marksard/Keyboards/_image/oled01.jpg

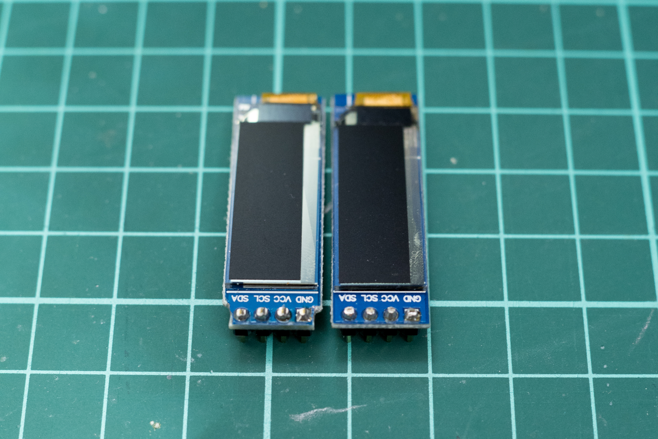
_image/oled01.jpg
