marksard/Keyboards/leftover30/documents/_image/case.png

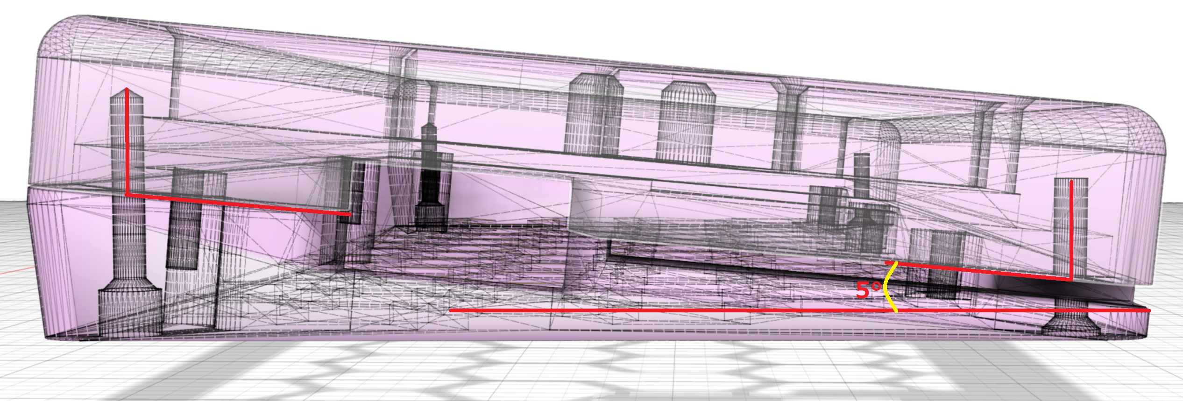
leftover30/documents/_image/case.png
