marksard/Keyboards/leftover30/documents/_image/case_bottom.jpg

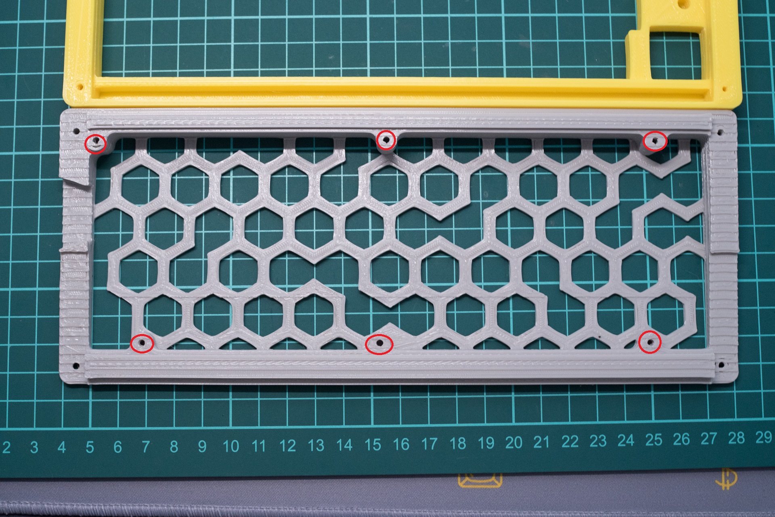
leftover30/documents/_image/case_bottom.jpg
