marksard/Keyboards/leftover30/documents/_image/case_ins1.jpg

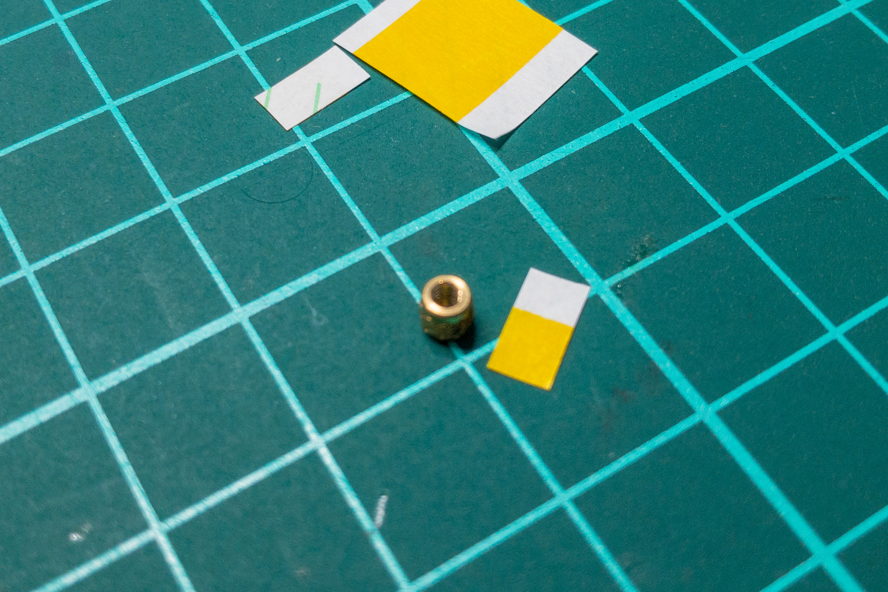
leftover30/documents/_image/case_ins1.jpg
