marksard/Keyboards/leftover30/documents/_image/case_ins2.jpg

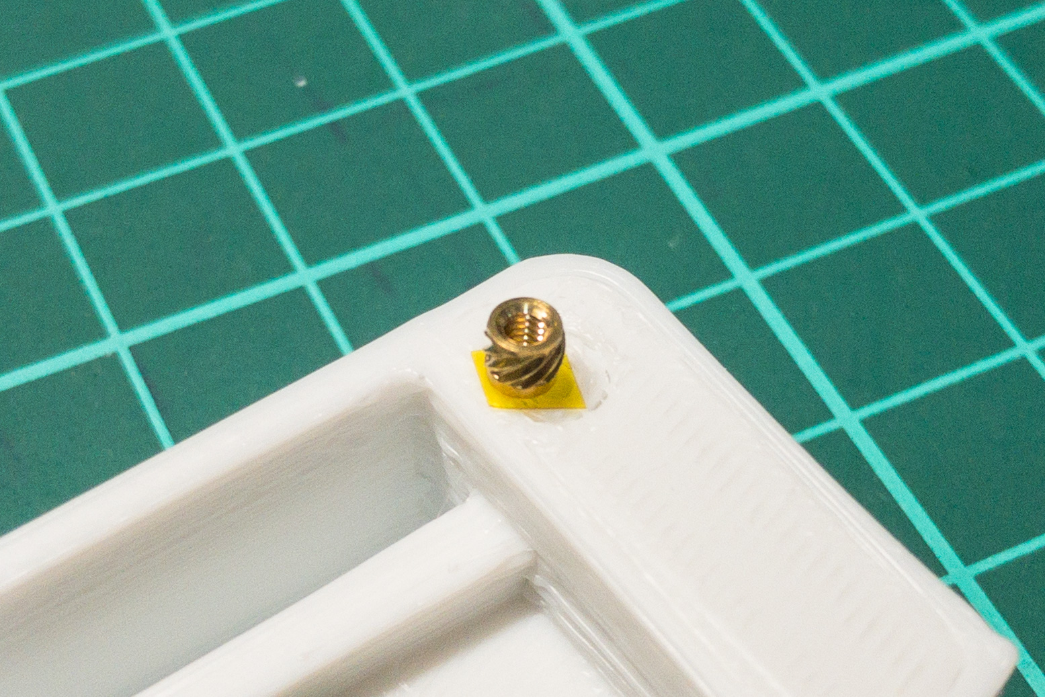
leftover30/documents/_image/case_ins2.jpg
