marksard/Keyboards/leftover30/documents/_image/case_top.jpg

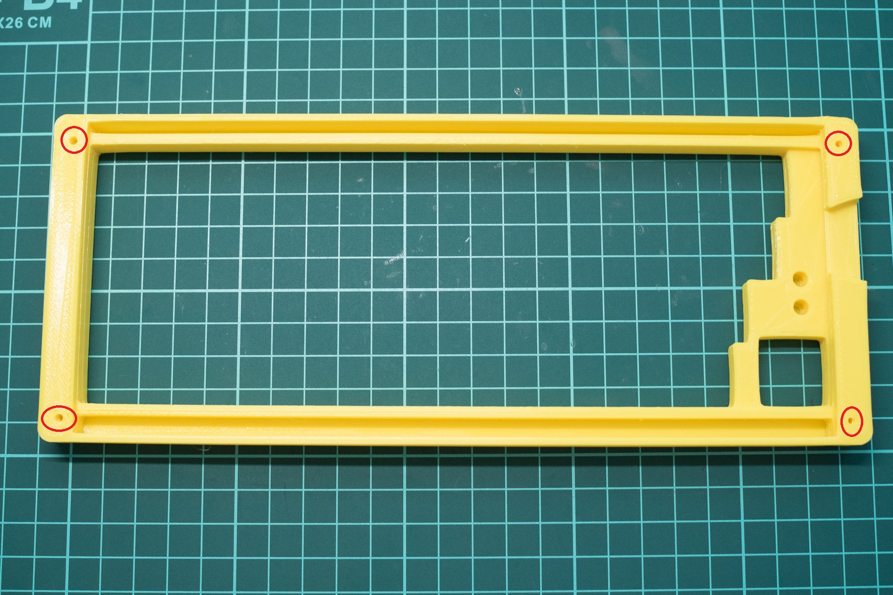
leftover30/documents/_image/case_top.jpg
