marksard/Keyboards/leftover30/documents/_image/diode2.jpg

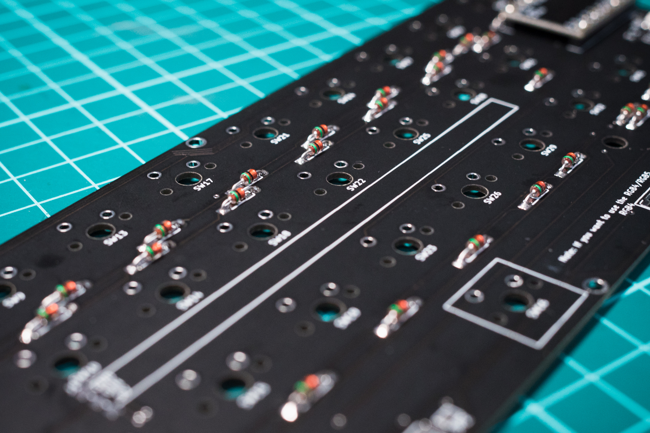
leftover30/documents/_image/diode2.jpg
