marksard/Keyboards/leftover30/documents/_image/led4.jpg

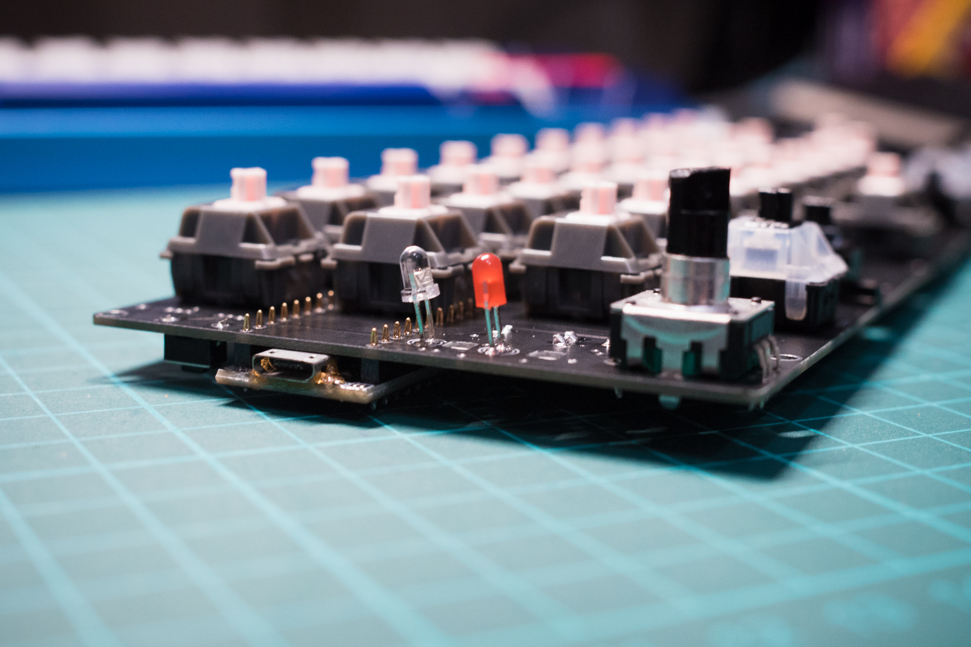
leftover30/documents/_image/led4.jpg
