marksard/Keyboards/leftover30/documents/_image/led.jpg

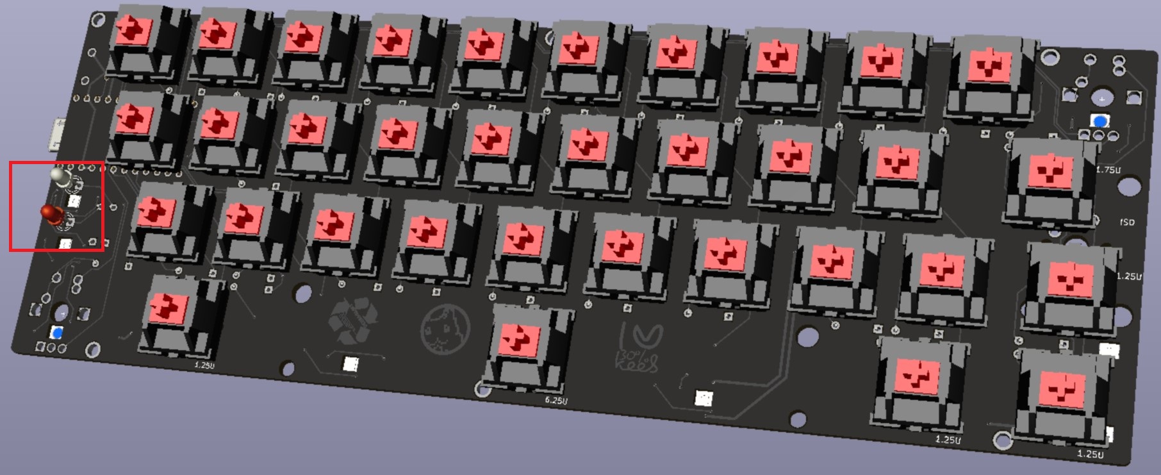
leftover30/documents/_image/led.jpg
