marksard/Keyboards/leftover30/documents/_image/re_cover.jpg

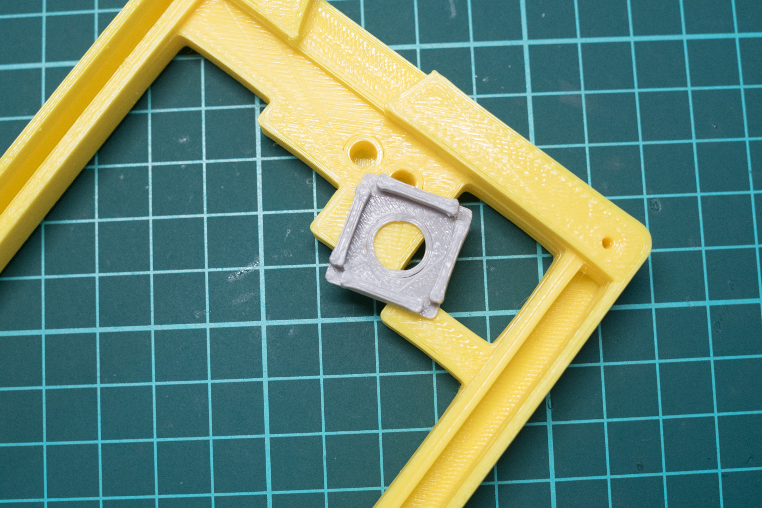
leftover30/documents/_image/re_cover.jpg
