marksard/Keyboards/leftover30/documents/_image/register2.jpg

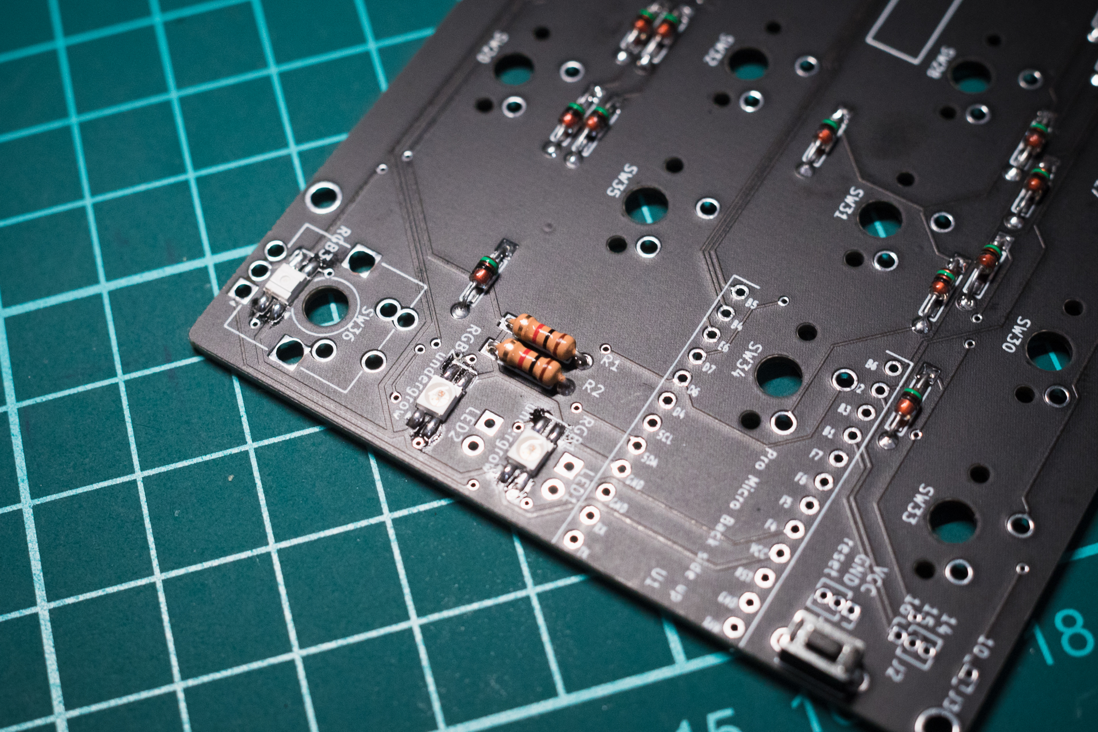
leftover30/documents/_image/register2.jpg
