marksard/Keyboards/leftover30/documents/_image/reset.jpg

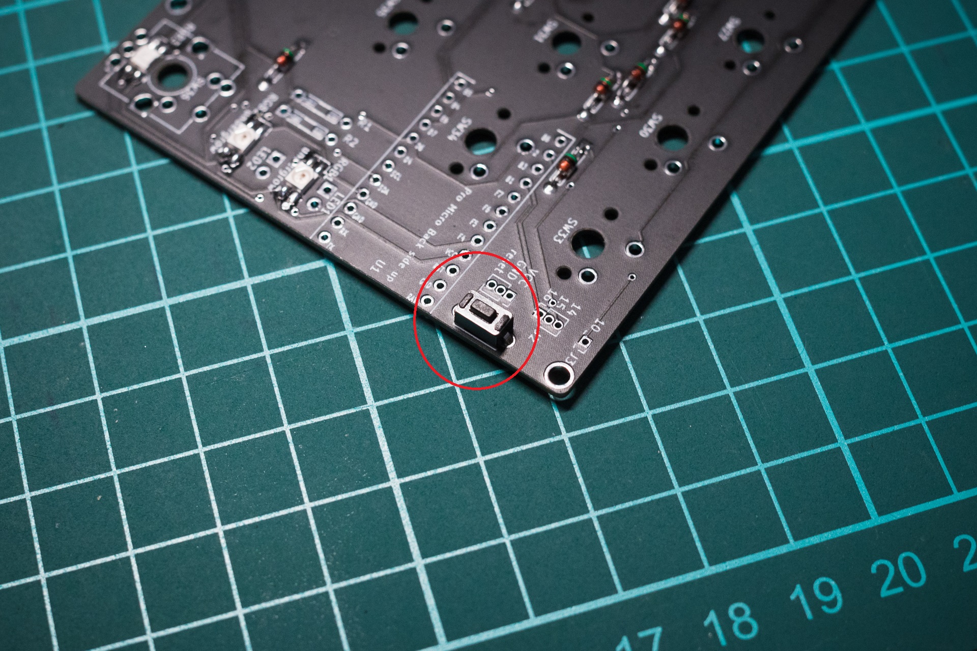
leftover30/documents/_image/reset.jpg
