marksard/Keyboards/leftover30/documents/_image/sk6812mini-e2.jpg

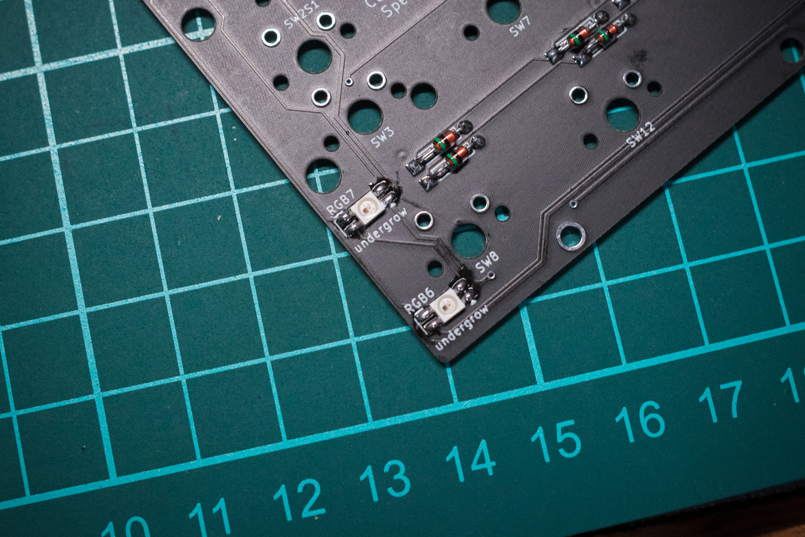
leftover30/documents/_image/sk6812mini-e2.jpg
