marksard/Keyboards/leftover30/documents/_image/stab2.jpg

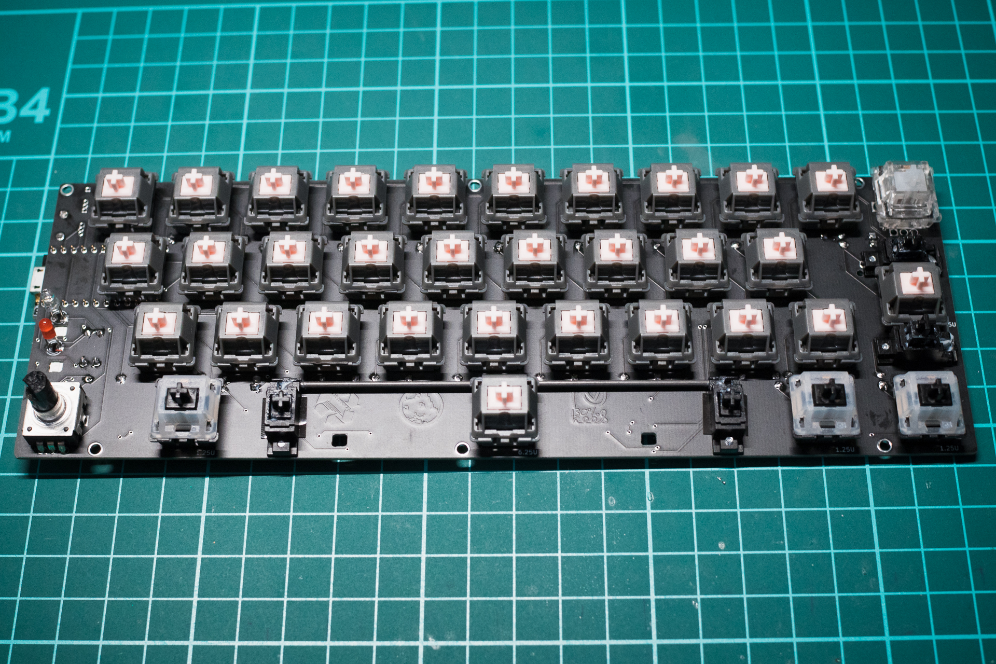
leftover30/documents/_image/stab2.jpg
