marksard/Keyboards/leftover30/documents/_image/sw_promicro2.jpg

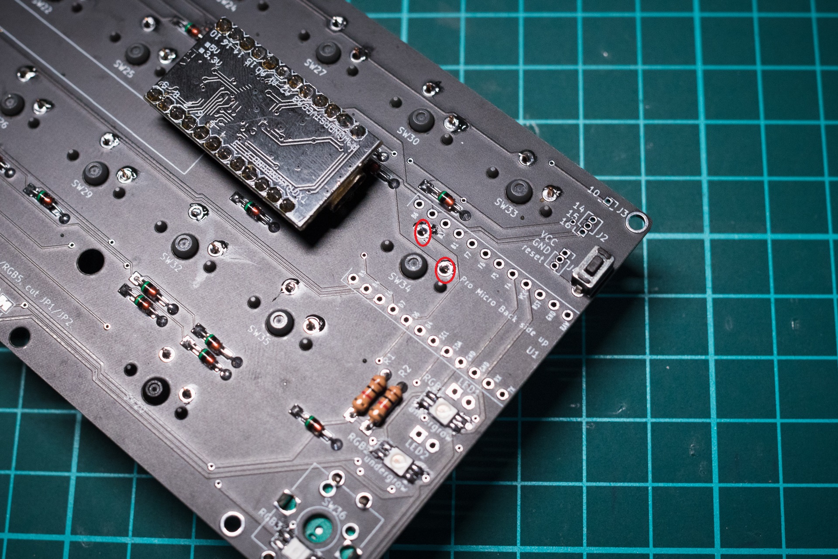
leftover30/documents/_image/sw_promicro2.jpg
