marksard/Keyboards/rhymestone/documents/_image/30key.png

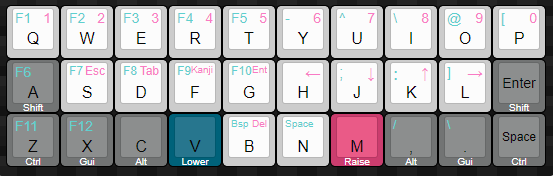
rhymestone/documents/_image/30key.png
