marksard/Keyboards/rhymestone/documents/_image/20181212-PC120072.jpg

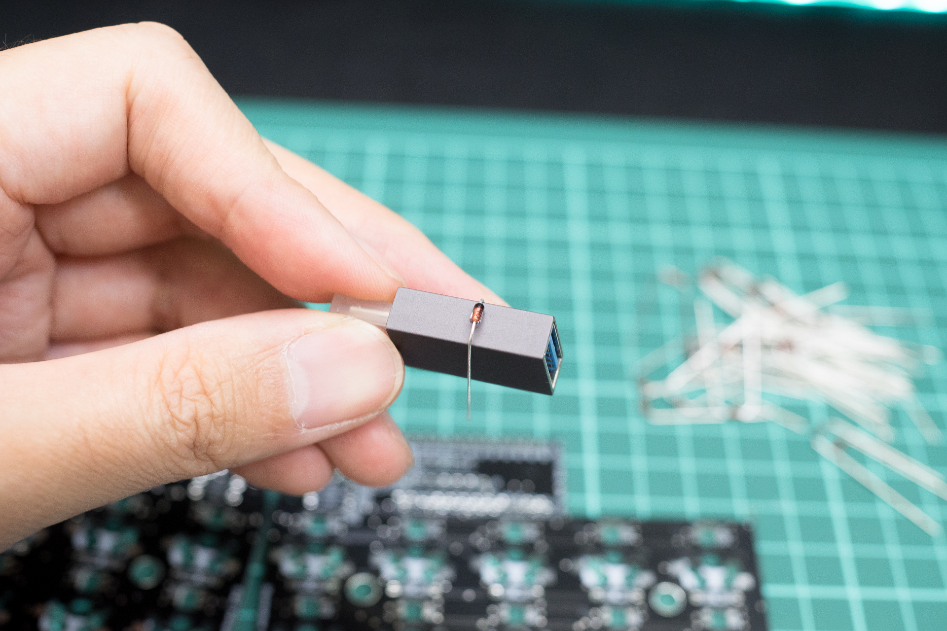
rhymestone/documents/_image/20181212-PC120072.jpg
