marksard/Keyboards/rhymestone/documents/_image/20181212-PC120073.jpg

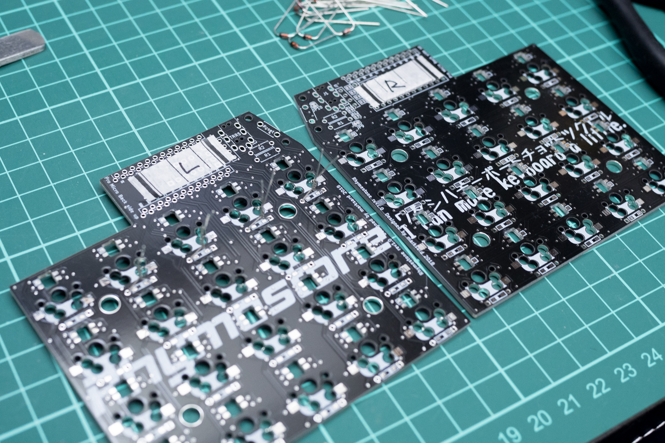
rhymestone/documents/_image/20181212-PC120073.jpg
