marksard/Keyboards/rhymestone/documents/_image/20181212-PC120074.jpg

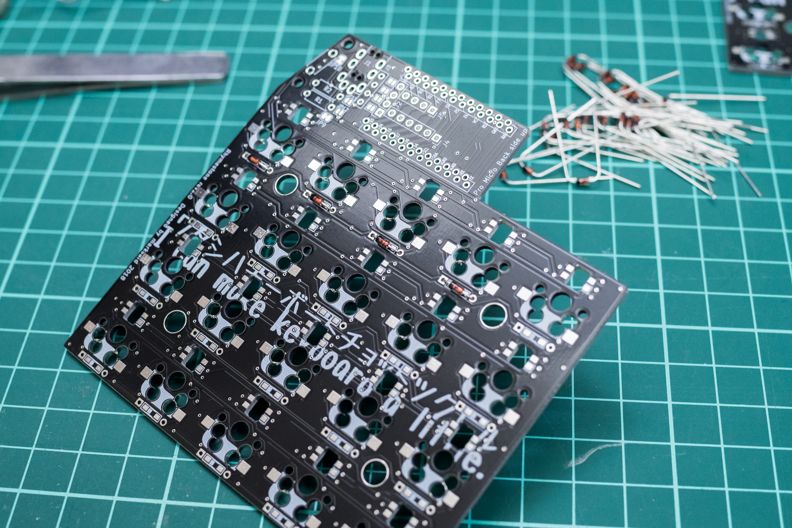
rhymestone/documents/_image/20181212-PC120074.jpg
