marksard/Keyboards/rhymestone/documents/_image/20181212-PC120074_2.jpg

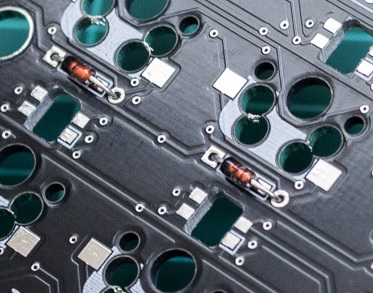
rhymestone/documents/_image/20181212-PC120074_2.jpg
