marksard/Keyboards/rhymestone/documents/_image/20181212-PC120075.jpg

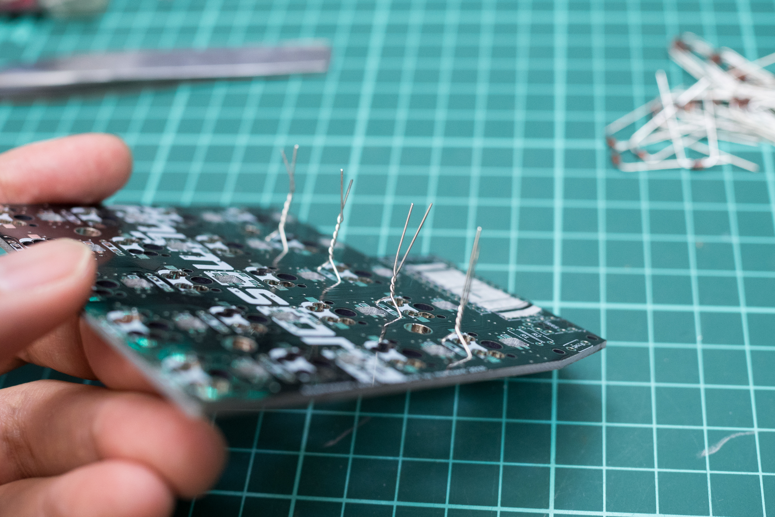
rhymestone/documents/_image/20181212-PC120075.jpg
