marksard/Keyboards/rhymestone/documents/_image/20181212-PC120088_2.jpg

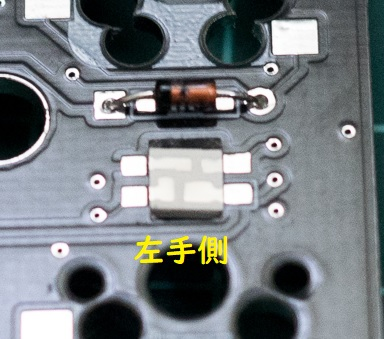
rhymestone/documents/_image/20181212-PC120088_2.jpg
