marksard/Keyboards/rhymestone/documents/_image/20181213-PC130101.jpg

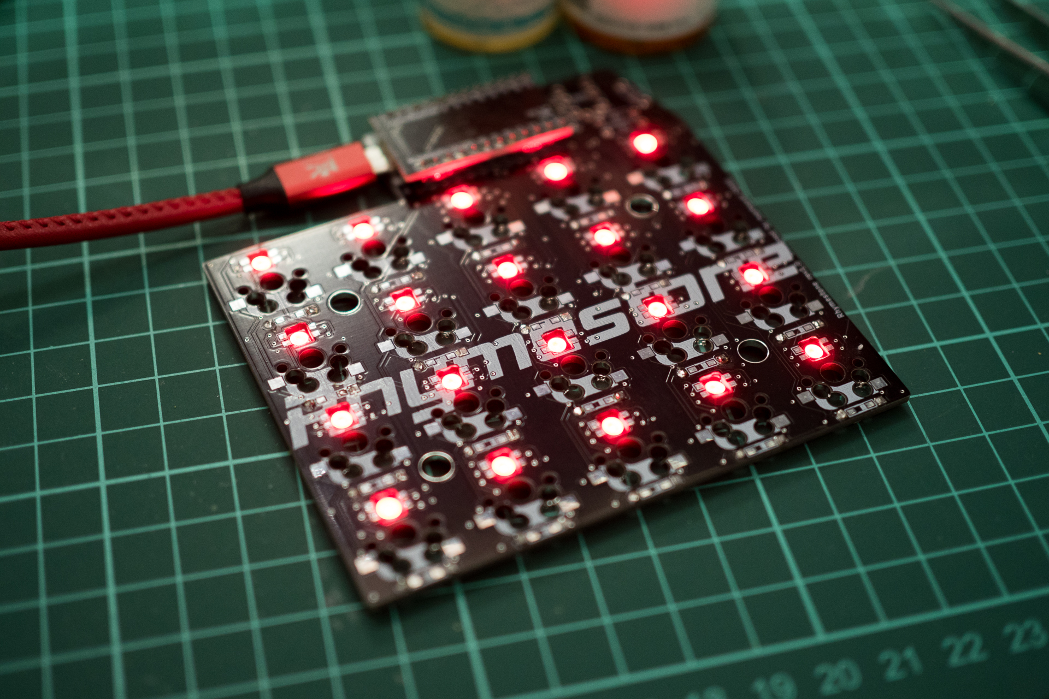
rhymestone/documents/_image/20181213-PC130101.jpg
