marksard/Keyboards/rhymestone/documents/_image/20181213-PC130107.jpg

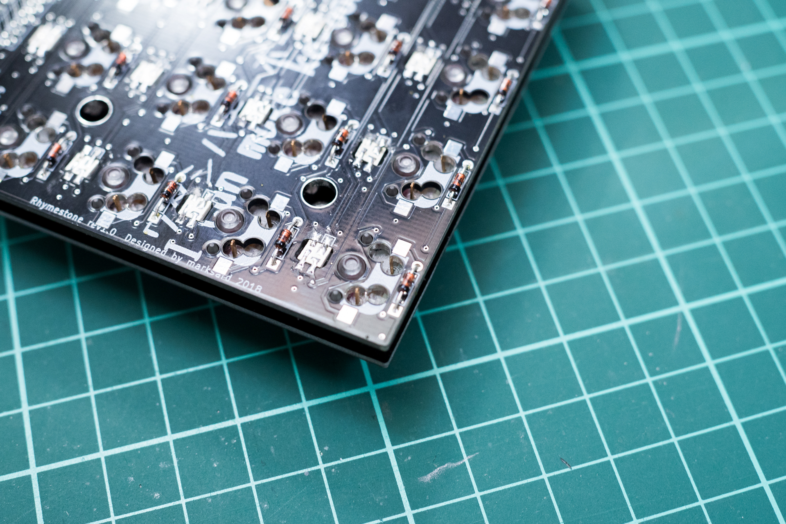
rhymestone/documents/_image/20181213-PC130107.jpg
