marksard/Keyboards/rhymestone/documents/_image/20181213-PC130111.jpg

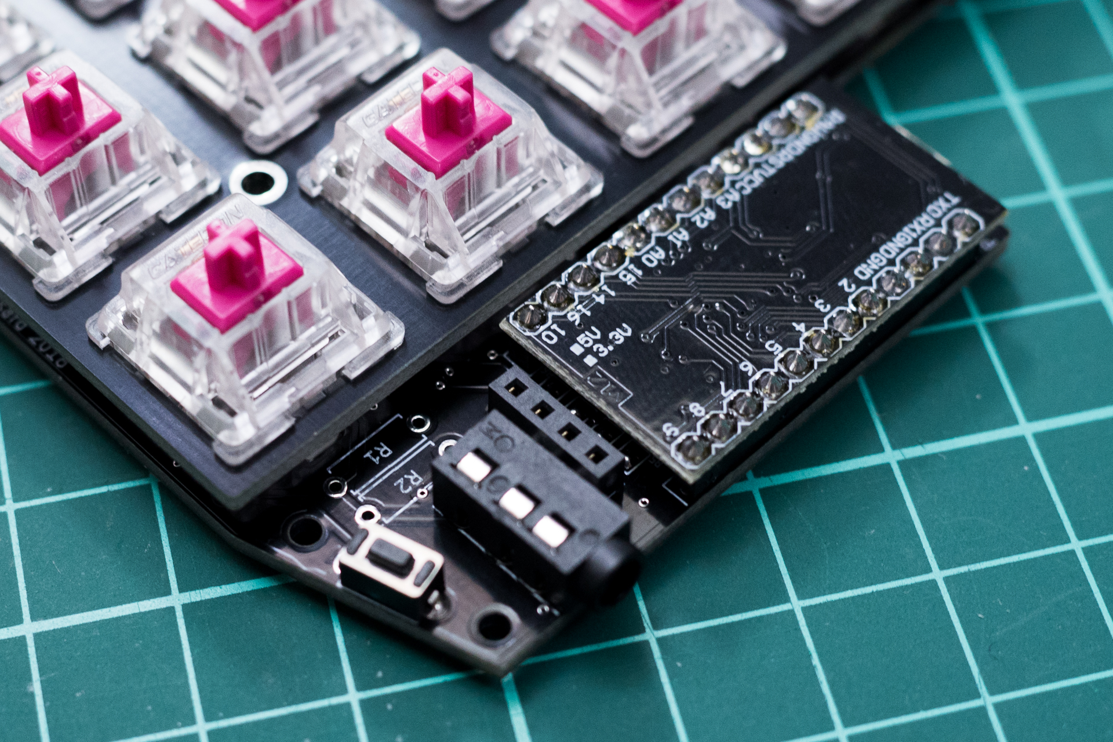
rhymestone/documents/_image/20181213-PC130111.jpg
