marksard/Keyboards/rhymestone/documents/_image/20181214-PC140118.jpg

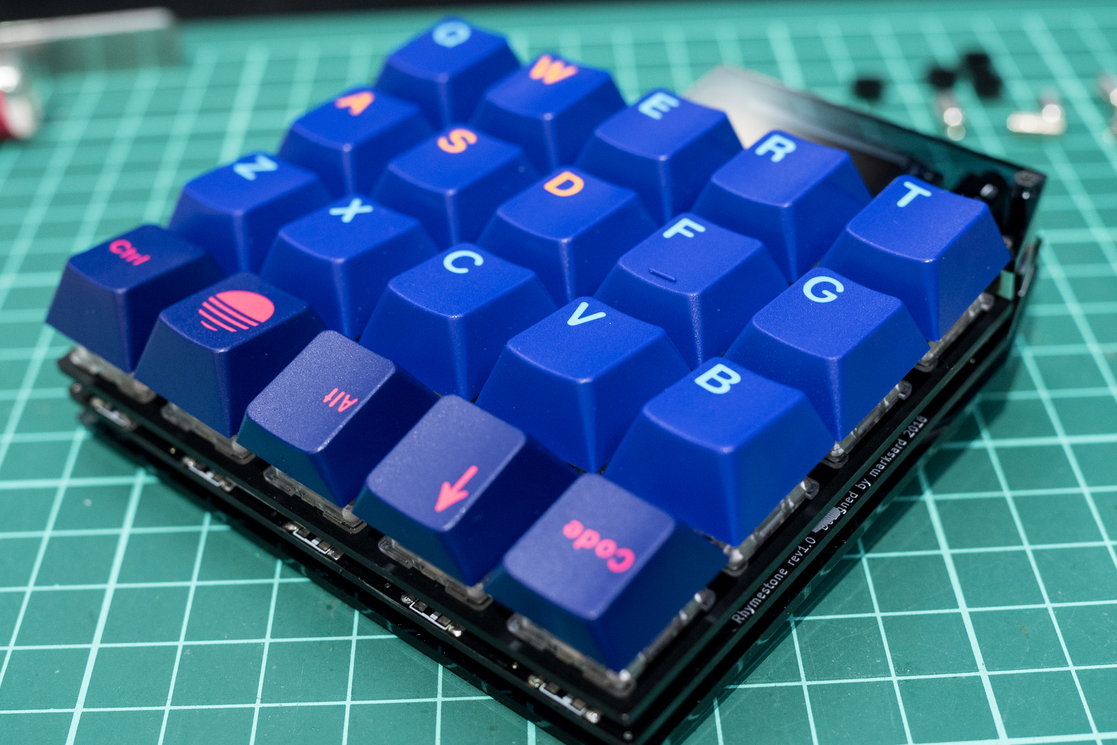
rhymestone/documents/_image/20181214-PC140118.jpg
