marksard/Keyboards/rhymestone/documents/_image/20181214-PC140120.jpg

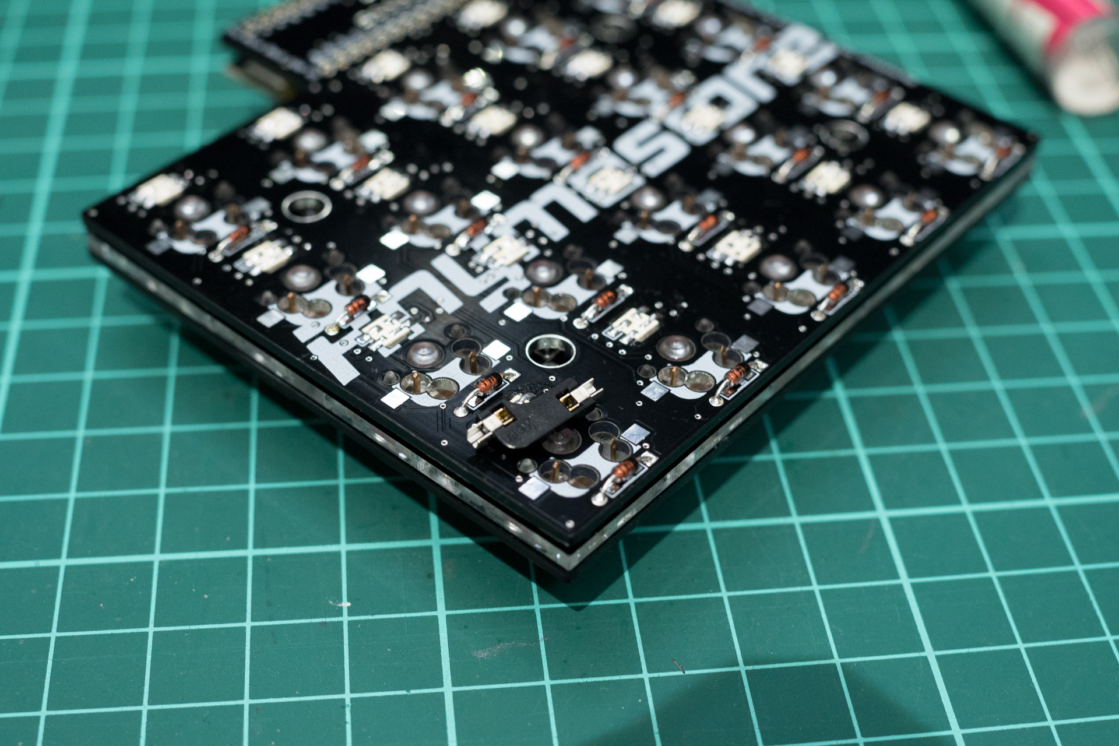
rhymestone/documents/_image/20181214-PC140120.jpg
