marksard/Keyboards/rhymestone/documents/_image/led_leftback.png

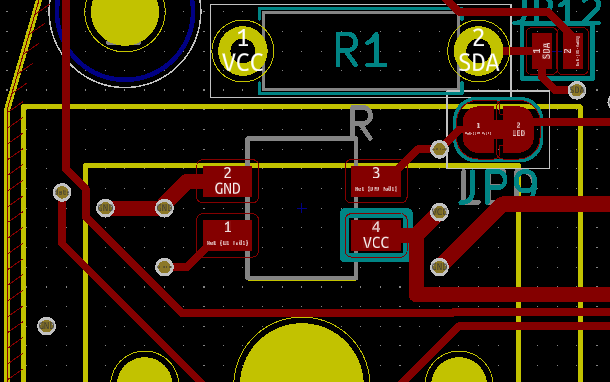
rhymestone/documents/_image/led_leftback.png
