marksard/Keyboards/rhymestone/documents/_image/led_rightback.png

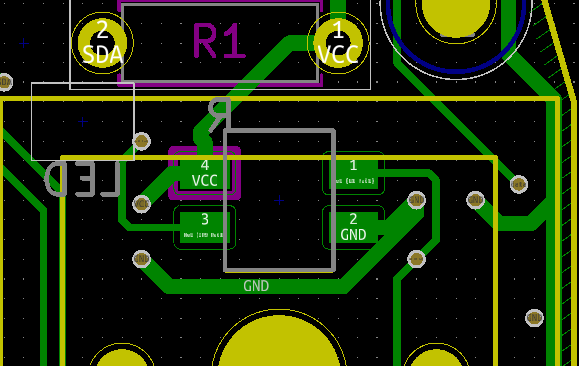
rhymestone/documents/_image/led_rightback.png
