marksard/Keyboards/rhymestone/documents/_image/ledmap.png

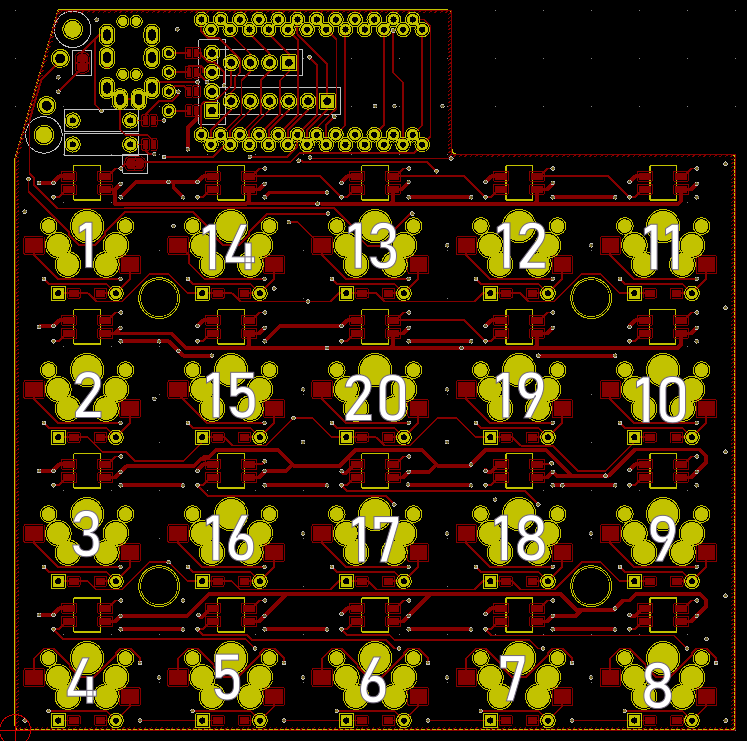
rhymestone/documents/_image/ledmap.png
