marksard/Keyboards/stonehenge30/documents/_image/20190202-P2020239.jpg

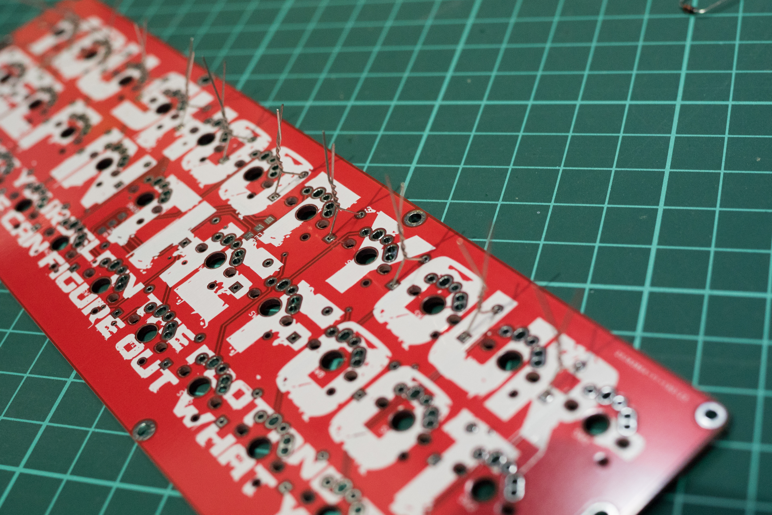
stonehenge30/documents/_image/20190202-P2020239.jpg
