marksard/Keyboards/stonehenge30/documents/_image/20190202-P2020255.jpg

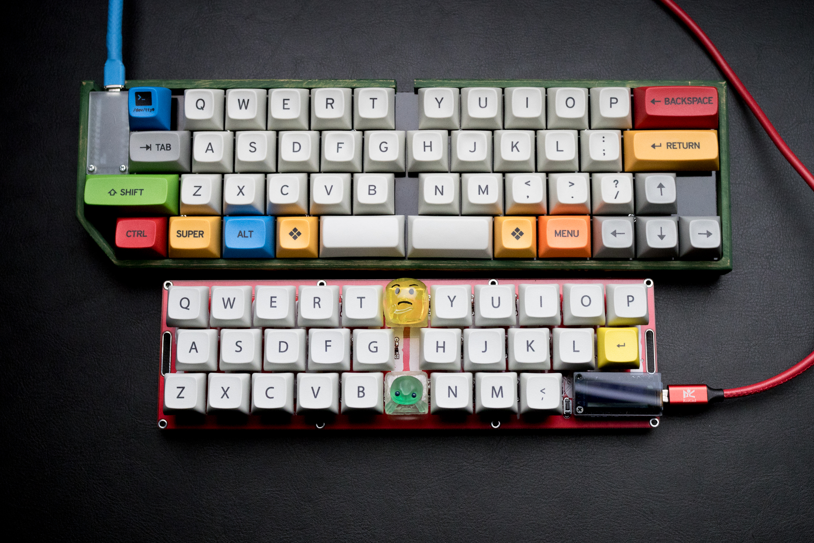
stonehenge30/documents/_image/20190202-P2020255.jpg
