marksard/Keyboards/stonehenge30/documents/_image/20190203-P2030266.jpg

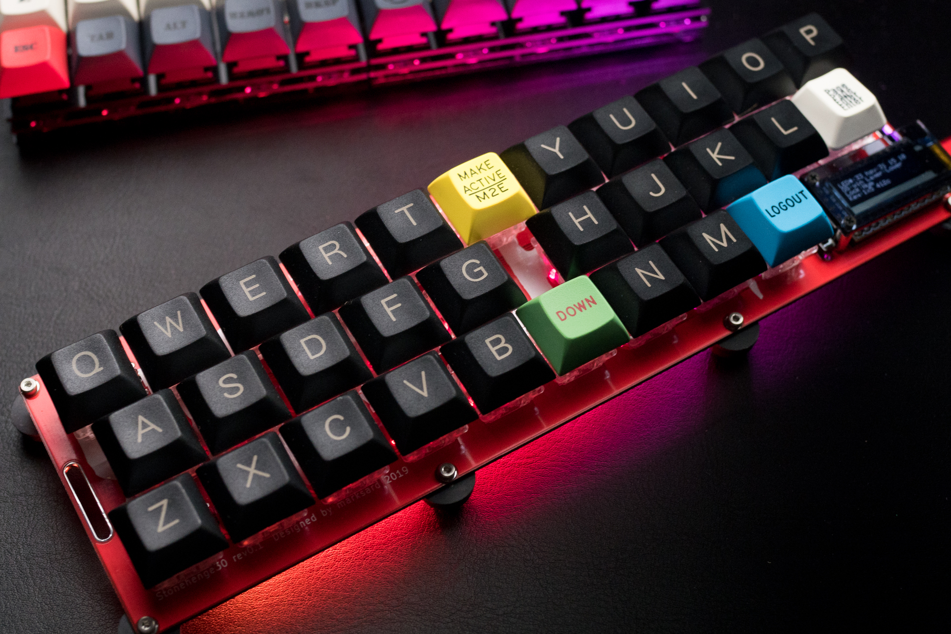
stonehenge30/documents/_image/20190203-P2030266.jpg
