marksard/Keyboards/stonehenge30/documents/_image/20190203-P2030276.jpg

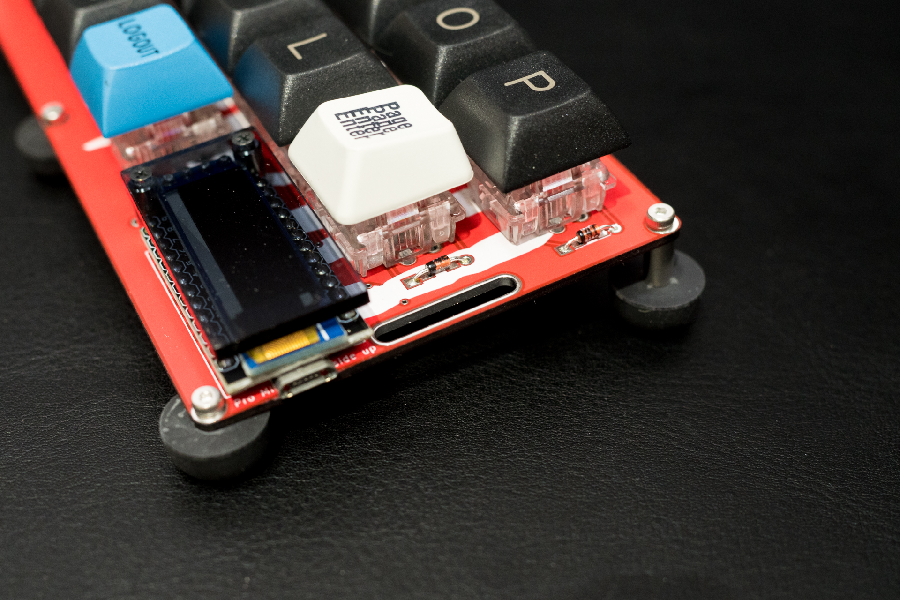
stonehenge30/documents/_image/20190203-P2030276.jpg
