marksard/Keyboards/stonehenge30/documents/_image/20190211-P2110297.jpg

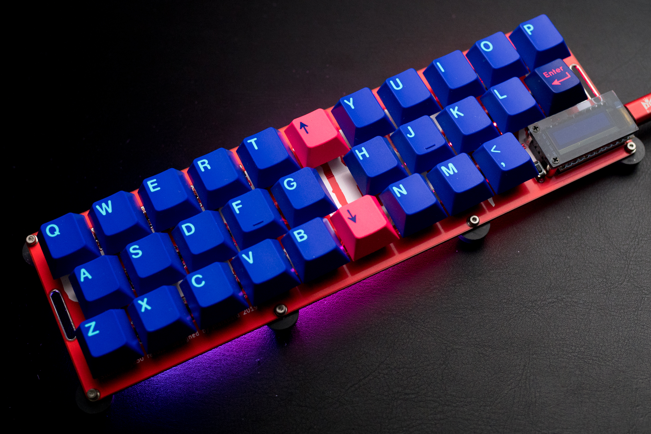
stonehenge30/documents/_image/20190211-P2110297.jpg
