marksard/Keyboards/stonehenge30/documents/_image/like_jis.png

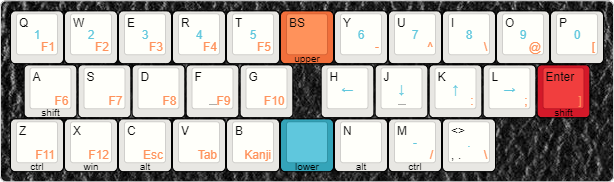
stonehenge30/documents/_image/like_jis.png
