marksard/Keyboards/treadstone32/documents/_image/20190424-P4240024.jpg

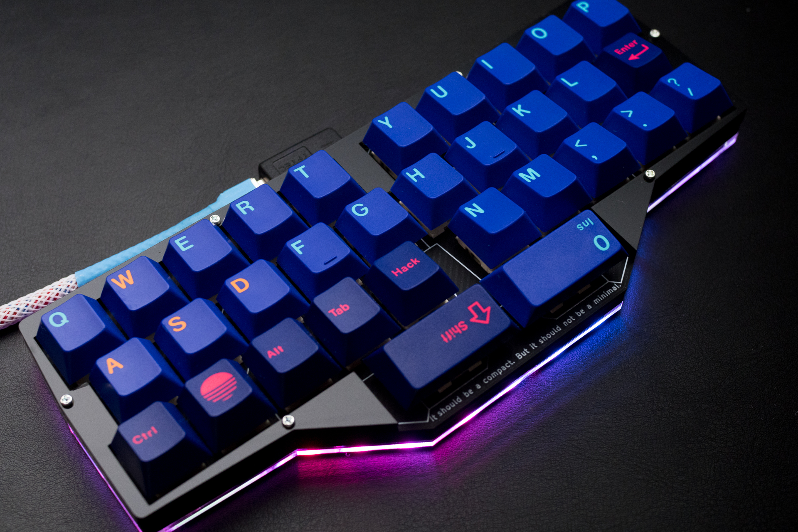
treadstone32/documents/_image/20190424-P4240024.jpg
