marksard/Keyboards/treadstone32/documents/_image/20200509-P5090002.jpg

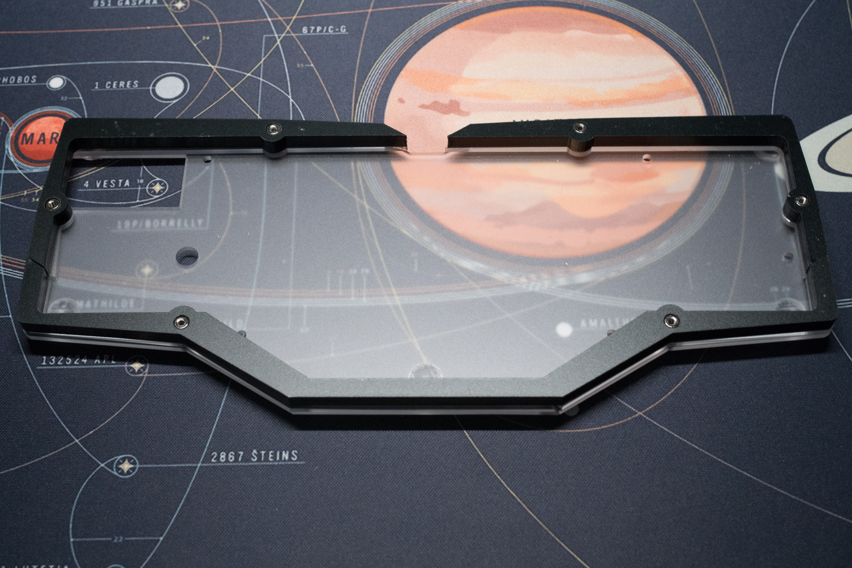
treadstone32/documents/_image/20200509-P5090002.jpg
