marksard/Keyboards/treadstone48/documents/_image/20181216-PC160171.jpg

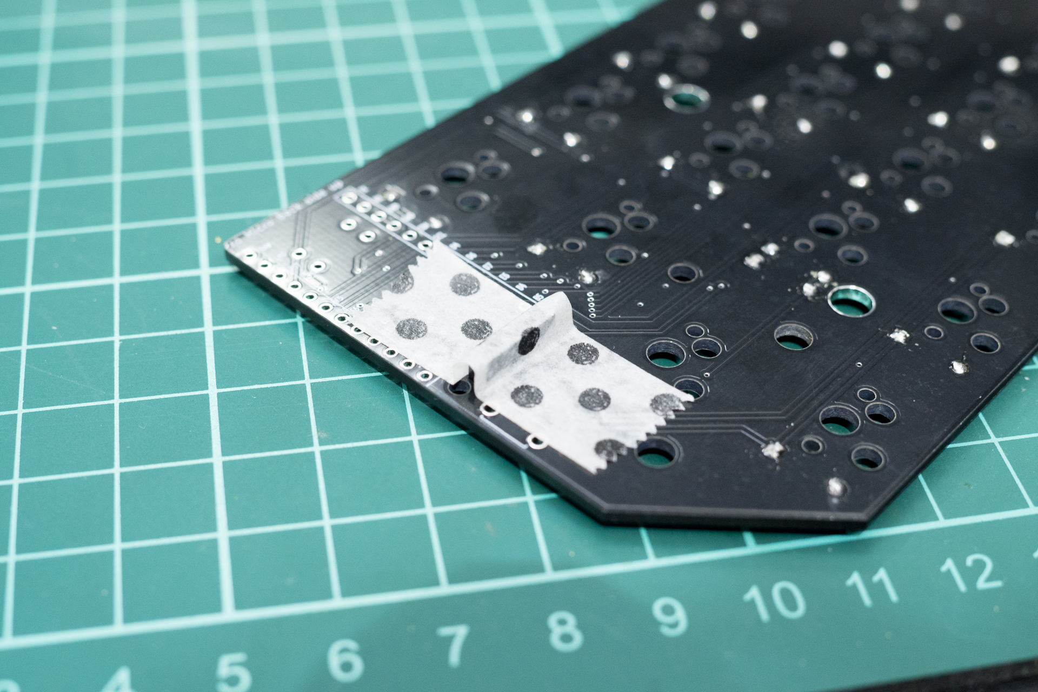
treadstone48/documents/_image/20181216-PC160171.jpg
