marksard/Keyboards/treadstone48/documents/_image/20181223-PC230004.jpg

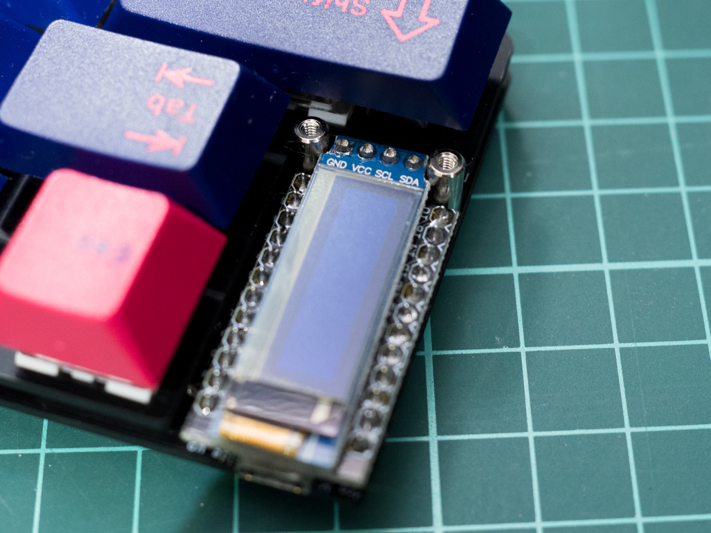
treadstone48/documents/_image/20181223-PC230004.jpg
