marksard/Keyboards/treadstone48/documents/_image/20181223-PC230005.jpg

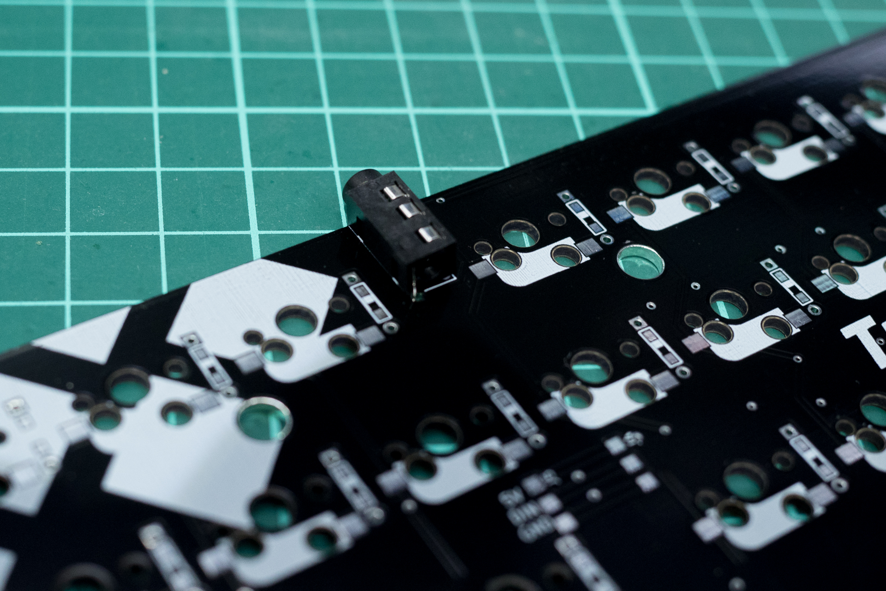
treadstone48/documents/_image/20181223-PC230005.jpg
