marksard/Keyboards/treadstone48/documents/_image/20200508-P5080006.jpg

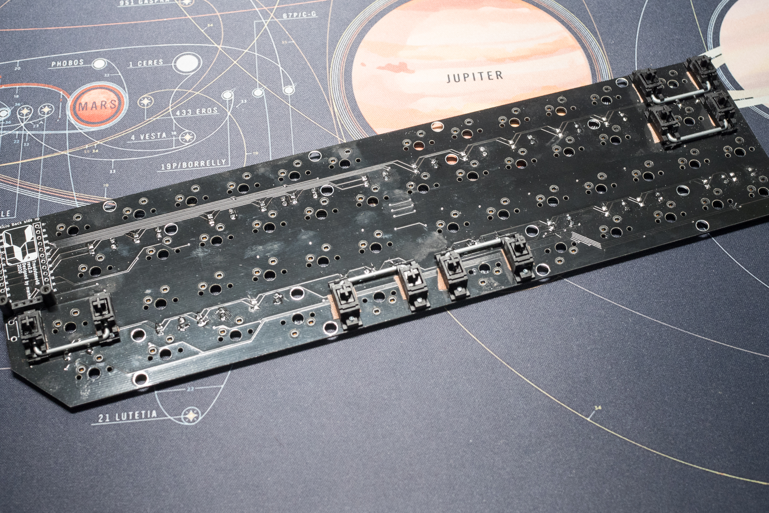
treadstone48/documents/_image/20200508-P5080006.jpg
