marksard/Keyboards/treadstone60/documents/_image/hkey_socket1.jpg

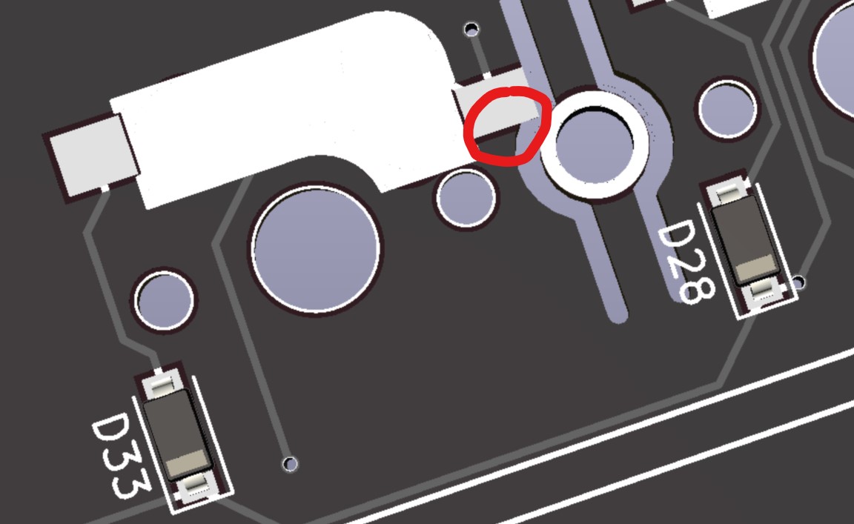
treadstone60/documents/_image/hkey_socket1.jpg
