marksard/Keyboards/treadstone60/documents/_image/right_shift.jpg

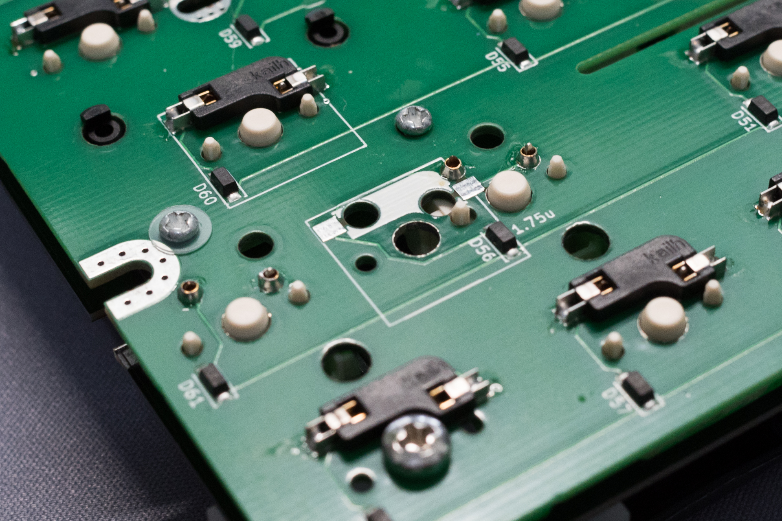
treadstone60/documents/_image/right_shift.jpg
